maboxi/Jodelautomat/JAVS-Schematics/Breadboard/AuxAdderInverterCircuit-Modified.asc

R1: res; 50k
R2: res; 50k
R3: res; 100k
R4: res; 100k
R5: res; 100k
R6: res; 100k
R8: res; 100k
U1: UniversalOpAmp
U2: UniversalOpAmp
V1: voltage; SINE(0 1 234 1)
V2: voltage; SINE(0 0.7 50)
V3: voltage; 3.3
V4: voltage; 5
V5: voltage; 5
Named nets: 0
.tran 0.1
