maboxi/Jodelautomat/Simulation/ChannelAdder_OffsetAndPotentiometer.asc

R1: res; 50k
R2: res; 50k
R3: res; 0
R4: res; 100k
R5: res; 100k
R6: res; 100k
R7: res; 100k
U1: UniversalOpAmp
U2: UniversalOpAmp
V1: voltage; SINE(0 0.9 50)
V2: voltage; SINE(0 0.3 234)
V3: voltage; 1.65
V4: voltage; 5V
V5: voltage; 5V
Named nets: 0
.tran 0.2
